takurx/ESP-Serial-Bridge/speed_test_script/test1_receive_random_com11.py

import serial, time

ser = serial.Serial("COM11", 115200)
# ser = serial.Serial("COM25", 115200)
# ser = serial.Serial("COM26", 115200)
# ser = serial.Serial("COM3", 115200)
# ser = serial.Serial("COM6", 115200)
# ser = serial.Serial("COM11", 115200)

count = 0
start = time.time()

while True:
    data = ser.read(1024)
    count += len(data)
    elapsed = time.time() - start
    if elapsed >= 1.0:
        # kbps = (count / elapsed) / 1024.0   # KB/s
        byte_per_sec = (count / elapsed)
        kbps = byte_per_sec/ 1024.0   # KB/s
        data_bps = byte_per_sec * 8          # データ部のみ（8bit換算）
        total_bps = byte_per_sec * 10        # UART全体（8N1の場合）
        # print(f"{kbps:.2f} KB/s")
        # print(f"{data_bps:.2f} bps")
        print(f"{total_bps:.2f} bps")
        count = 0
        start = time.time()
