takurx/ESP-Serial-Bridge/speed_test_script/test1_send_random_com12.py

import serial, os

# COMポートを指定（例: COM3）
# ser = serial.Serial("COM3", 115200)
# ser = serial.Serial("COM6", 115200)
# ser = serial.Serial("COM11", 115200)
# ser = serial.Serial("COM24", 115200)
ser = serial.Serial("COM12", 115200)
# ser = serial.Serial("COM26", 115200)

while True:
    ser.write(os.urandom(1024))
